Roversa-Robotics/robot-chassis-3dp/exports/stl/extras/bumper/pen-clamp-screw.stl

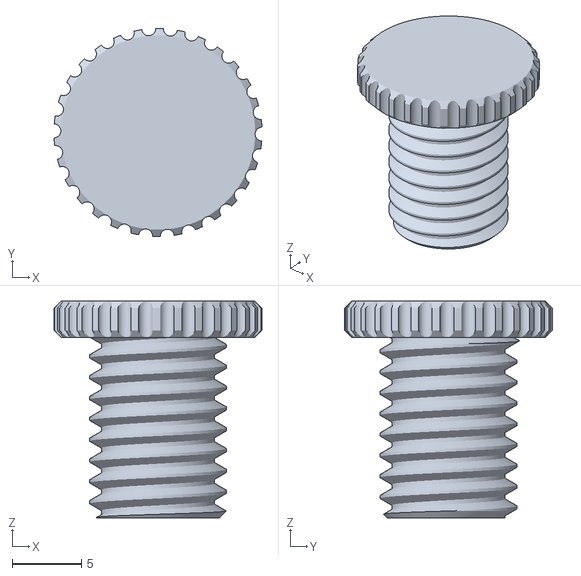
[picture p16: CAD file, 2026-09-24]
exports/stl/extras/bumper/pen-clamp-screw.stl
15.0 x 15.0 x 15.6
